denisaangelescu/Voltage_Regulator/Simulations/deriva_termica_set=0.jpg

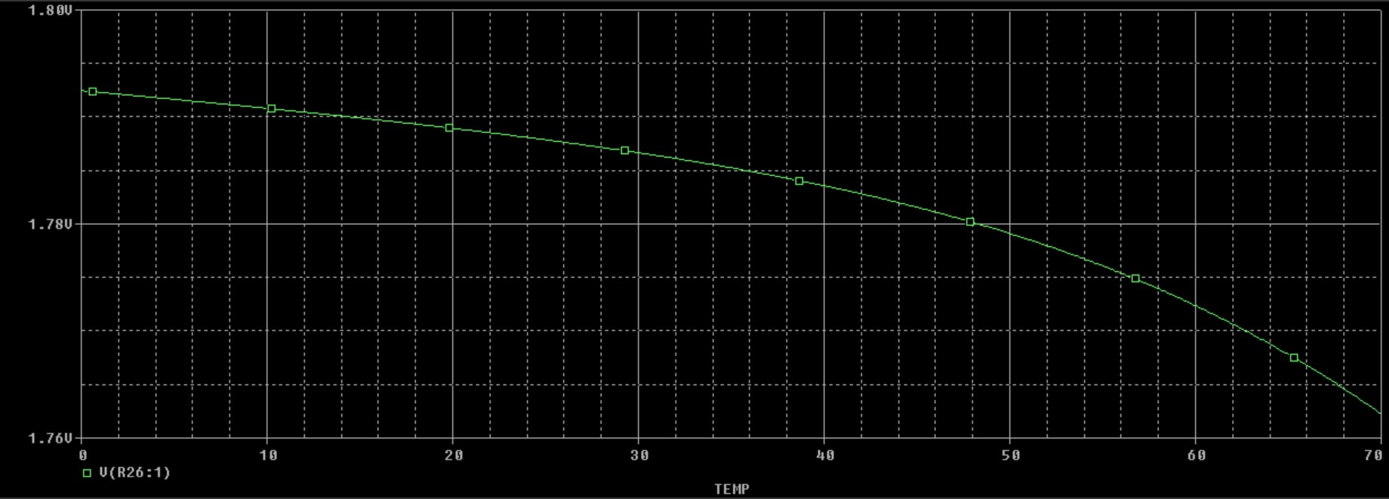
Simulations/deriva_termica_set=0.jpg
