denisaangelescu/Voltage_Regulator/Simulations/protectie_temperatura_set=0.jpg

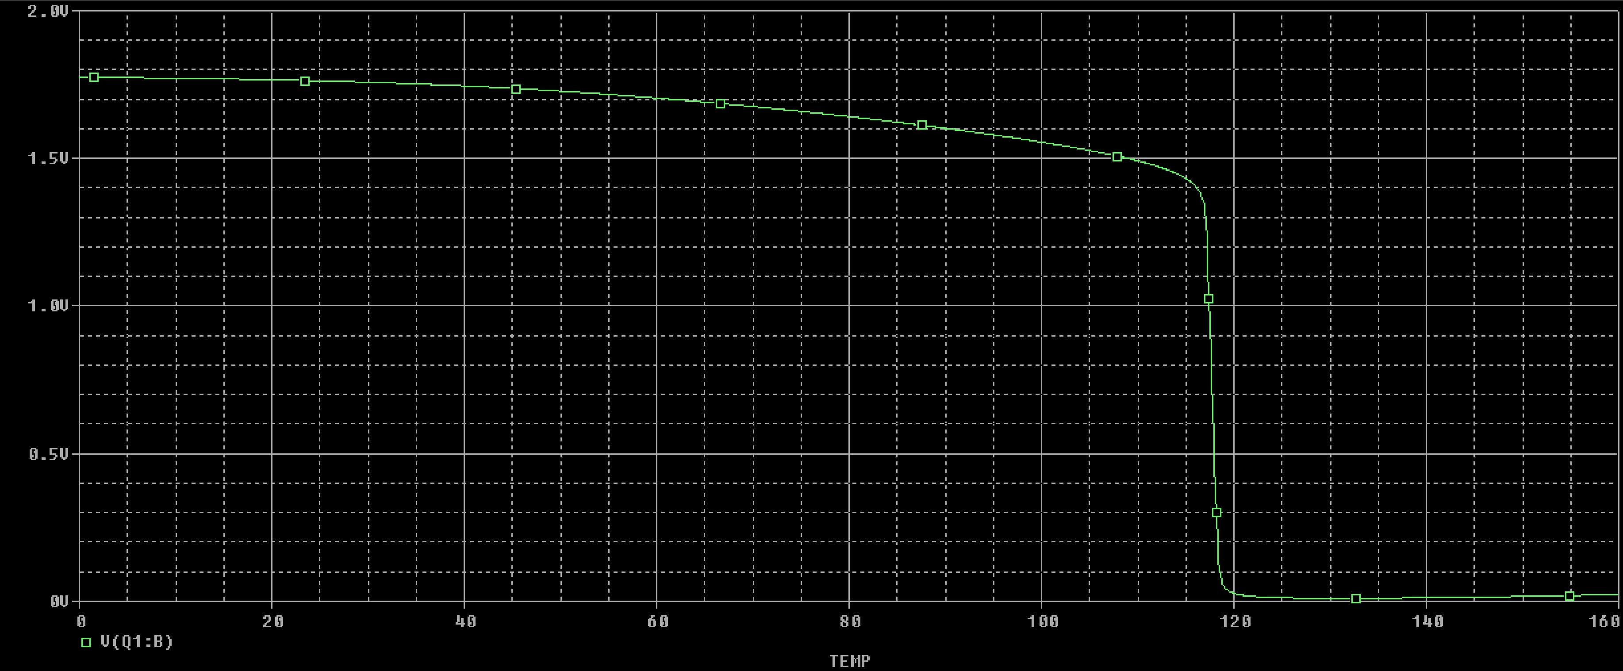
Simulations/protectie_temperatura_set=0.jpg
