denisaangelescu/Voltage_Regulator/Simulations/protectie_temperatura_set=1.jpg

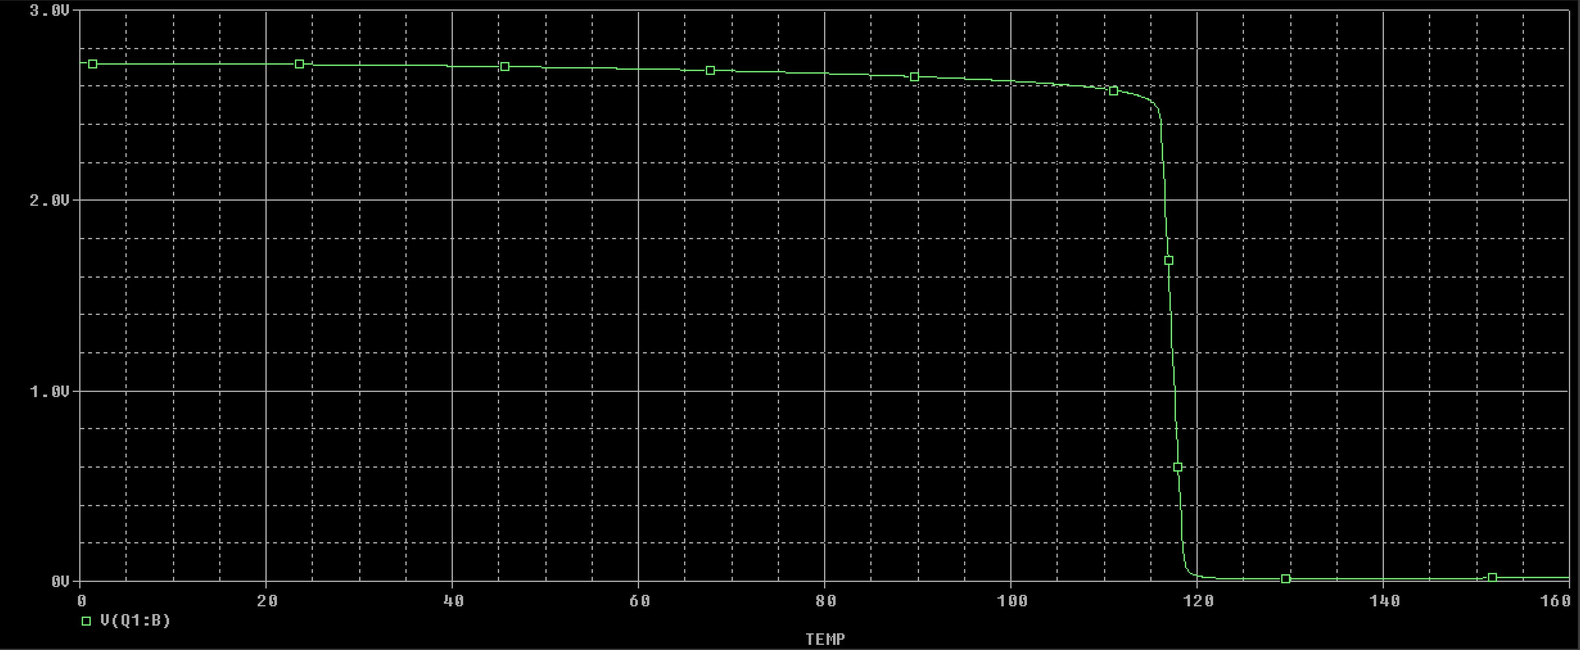
Simulations/protectie_temperatura_set=1.jpg
