denisaangelescu/Voltage_Regulator/Simulations/psrr.jpg

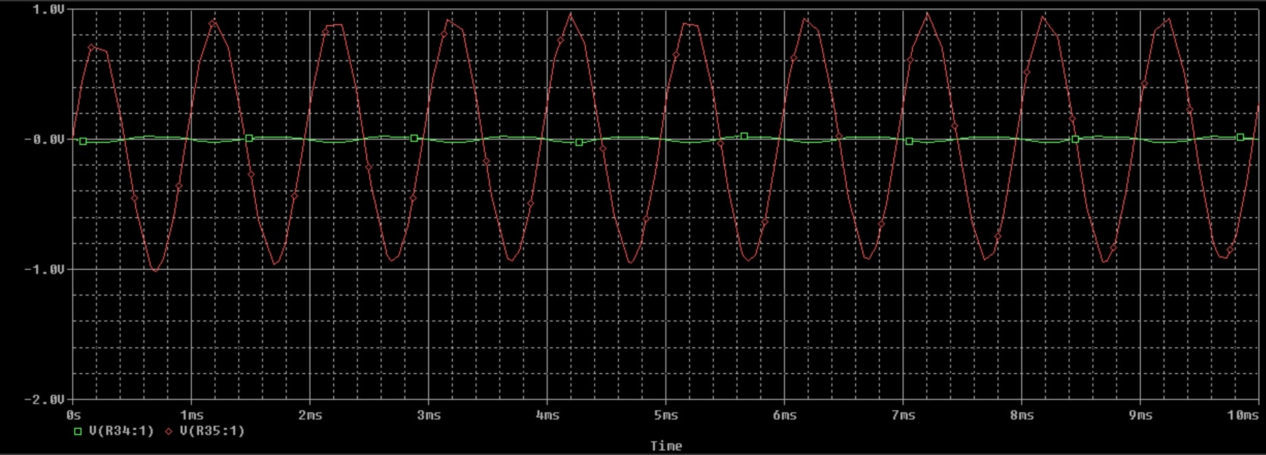
Simulations/psrr.jpg
