denisaangelescu/Voltage_Regulator/Simulations/stabilitate_cu_vin_set=0.jpg

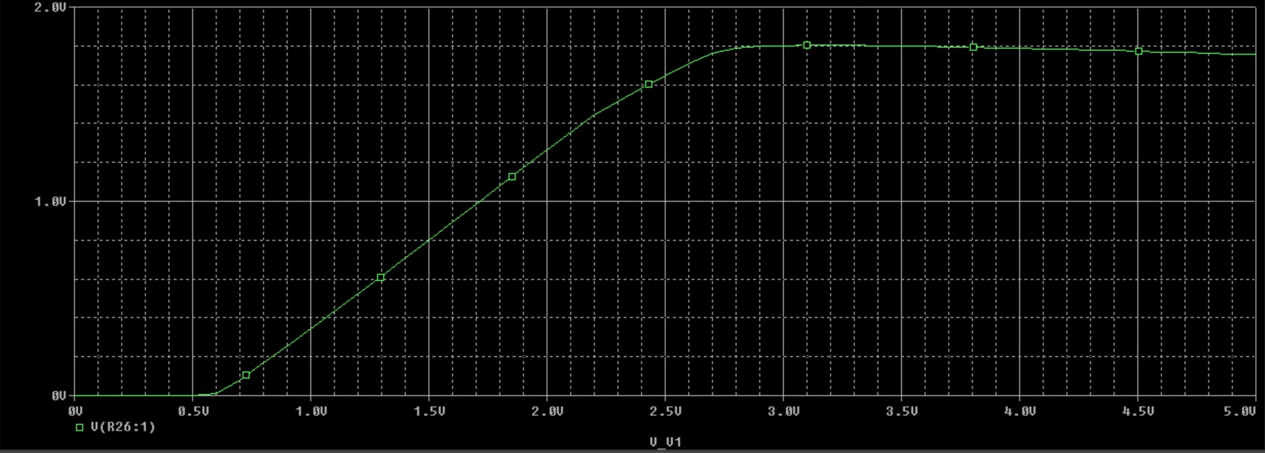
Simulations/stabilitate_cu_vin_set=0.jpg
